ionutms/Minimal_LT8304/minimal_lt8304/docs/pictures/4_minimal_lt8304_left.png

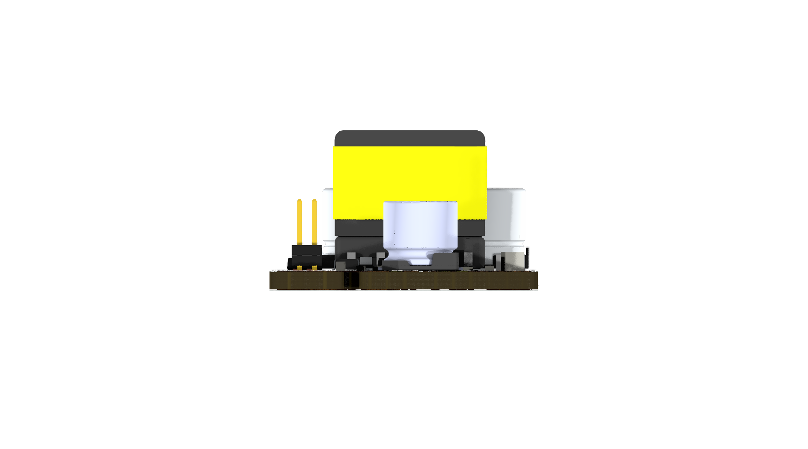
minimal_lt8304/docs/pictures/4_minimal_lt8304_left.png
